Physics-Dude/Phys-Index-EyetrackVR-HW/Gum Stick Remix for 3x ESPs plus USB Hub/Adafruit USB Hub (Latest Version)/Prototypes (Work In Progress)/GSR-Adafruit_Lid-Cover-USB (M3x20mm).3mf

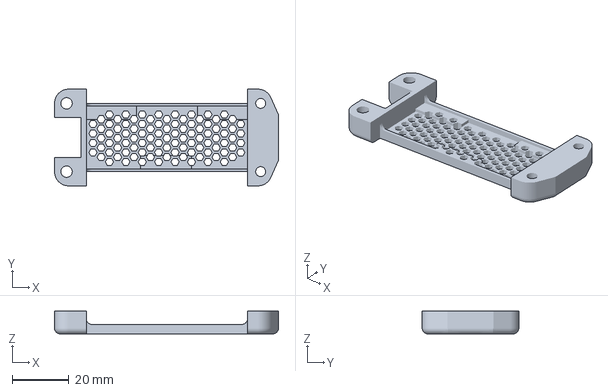
[picture p15: CAD file, 2025-03-30]
Gum Stick Remix for 3x ESPs plus USB Hub/Adafruit USB Hub (Latest Version)/Prototypes (Work In Progress)/GSR-Adafruit_Lid-Cover-USB (M3x20mm).3mf
78.8 x 34.0 x 8.00 mm
