Physics-Dude/Phys-Index-EyetrackVR-HW/Gum Stick Remix for 3x ESPs plus USB Hub/Frunk Holder (Use M3x14mm Lid)/GSR-Frunk_Brace_NoCam.3mf

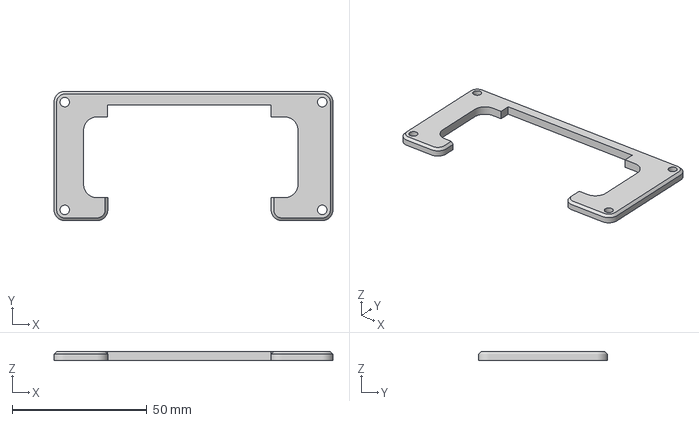
[picture p16: CAD file, 2025-03-11]
Gum Stick Remix for 3x ESPs plus USB Hub/Frunk Holder (Use M3x14mm Lid)/GSR-Frunk_Brace_NoCam.3mf
103.6 x 48.0 x 3.32 mm
