Physics-Dude/Phys-Index-EyetrackVR-HW/Gum Stick Remix for 3x ESPs plus USB Hub/Origional GSR Design (Cheap USB Hub)/GSR-Origional_Hub-Frame.3mf

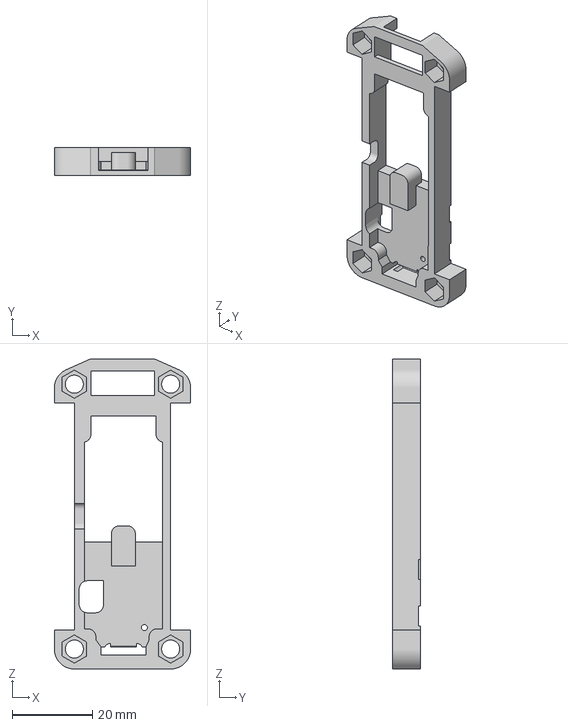
[picture p17: CAD file, 2025-03-11]
Gum Stick Remix for 3x ESPs plus USB Hub/Origional GSR Design (Cheap USB Hub)/GSR-Origional_Hub-Frame.3mf
34.0 x 7.00 x 77.3 mm
