Physics-Dude/Phys-Index-EyetrackVR-HW/Babble Face Tracker Cam-LED Mount/EXTENDED Face Mount arm v4 PRINT ME.stl

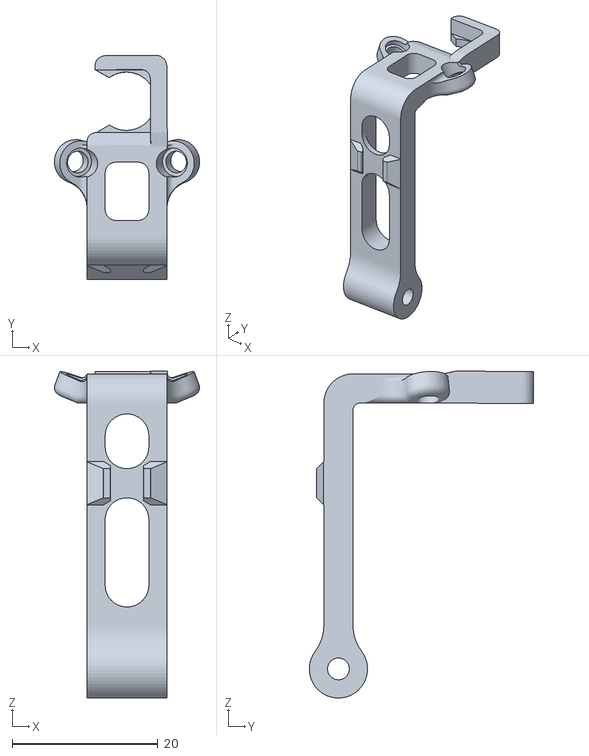
[picture p18: CAD file, 2023-12-08]
Babble Face Tracker Cam-LED Mount/EXTENDED Face Mount arm v4 PRINT ME.stl
19.9 x 30.8 x 44.9
