Physics-Dude/Phys-Index-EyetrackVR-HW/ETVR ValveIndex Cam-LED Mount Rings/Index-EyetrackVRv4 v18.step

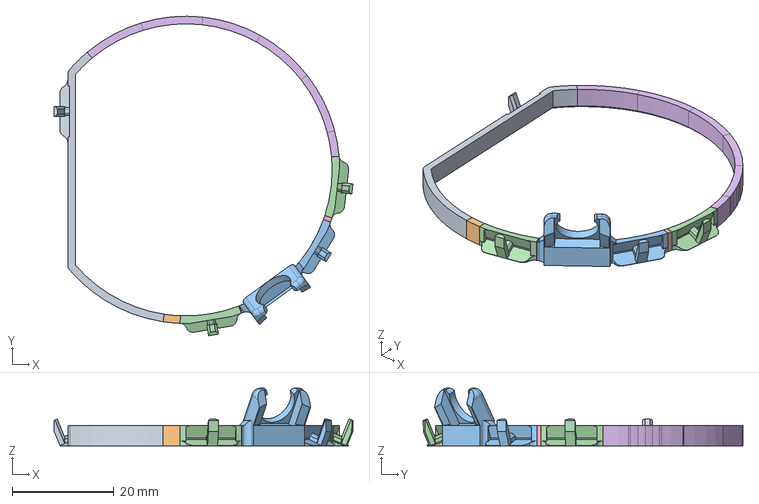
[picture p20: CAD file, 2023-10-20]
ETVR ValveIndex Cam-LED Mount Rings/Index-EyetrackVRv4 v18.step
58.9 x 62.9 x 11.4 mm
