Physics-Dude/Phys-Index-EyetrackVR-HW/Gum Stick Dongle Custom USB Hub Case/XIAO-ESP32S3 ETVR v4 gum stick index mount v22.step

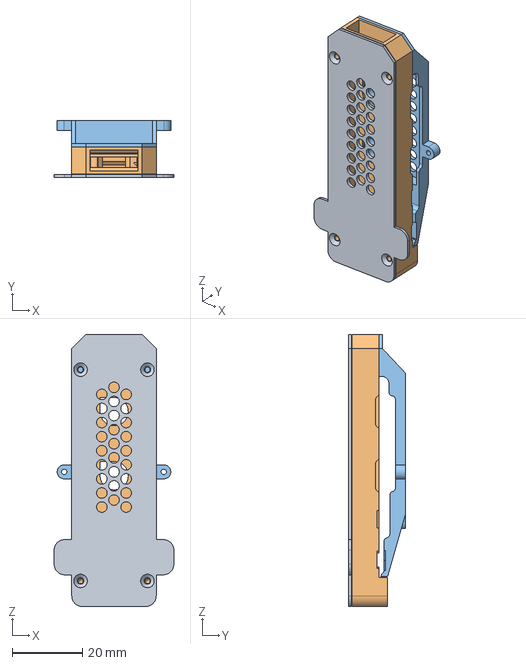
[picture p21: CAD file, 2023-10-27]
Gum Stick Dongle Custom USB Hub Case/XIAO-ESP32S3 ETVR v4 gum stick index mount v22.step
34.0 x 16.1 x 77.2 mm
