Physics-Dude/Phys-Index-EyetrackVR-HW/Gum Stick Remix for 3x ESPs plus USB Hub/Adafruit USB Hub (Latest Version)/GSR-Adafruit_Lid-Cover-Fill (M3x14mm).3mf

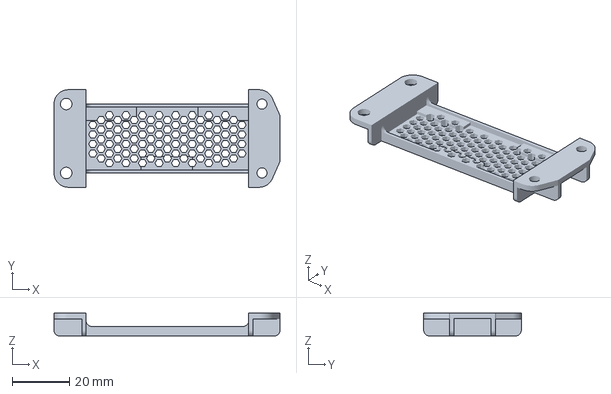
[picture p22: CAD file, 2025-03-30]
Gum Stick Remix for 3x ESPs plus USB Hub/Adafruit USB Hub (Latest Version)/GSR-Adafruit_Lid-Cover-Fill (M3x14mm).3mf
78.8 x 34.0 x 8.00 mm
