Physics-Dude/Phys-Index-EyetrackVR-HW/Gum Stick Remix for 3x ESPs plus USB Hub/Adafruit USB Hub (Latest Version)/Prototypes (Work In Progress)/GSR-Adafruit_Lid-USB-C (M3x14mm).3mf

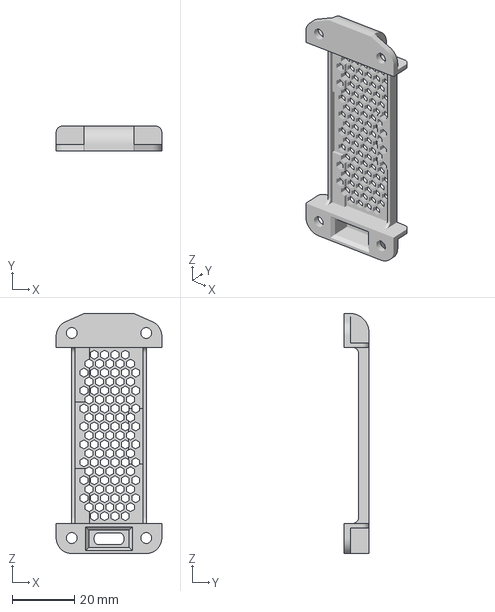
[picture p23: CAD file, 2025-03-11]
Gum Stick Remix for 3x ESPs plus USB Hub/Adafruit USB Hub (Latest Version)/Prototypes (Work In Progress)/GSR-Adafruit_Lid-USB-C (M3x14mm).3mf
34.0 x 8.00 x 77.3 mm
