Physics-Dude/Phys-Index-EyetrackVR-HW/Gum Stick Remix for 3x ESPs plus USB Hub/Frunk Holder (Use M3x14mm Lid)/GSR-Frunk_Brace_WithCam.3mf

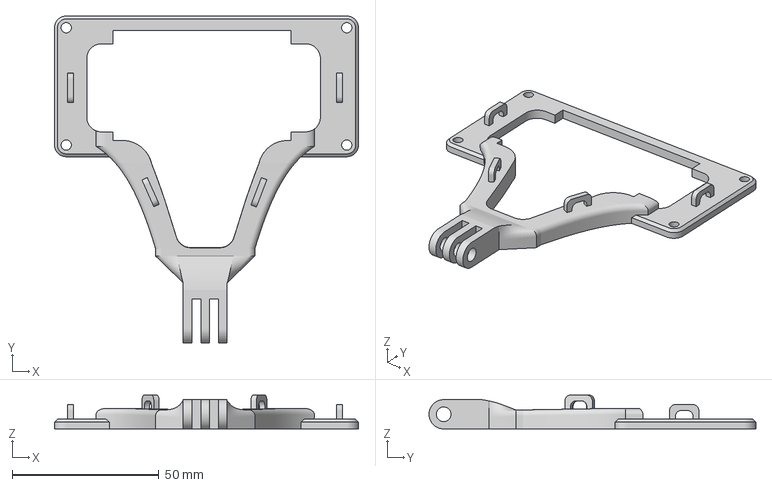
[picture p24: CAD file, 2025-03-11]
Gum Stick Remix for 3x ESPs plus USB Hub/Frunk Holder (Use M3x14mm Lid)/GSR-Frunk_Brace_WithCam.3mf
103.6 x 111.5 x 11.6 mm
