Physics-Dude/Phys-Index-EyetrackVR-HW/Babble Face Tracker Cam-LED Mount/FACE MOUNT v4 - PRINT ME with support.stl

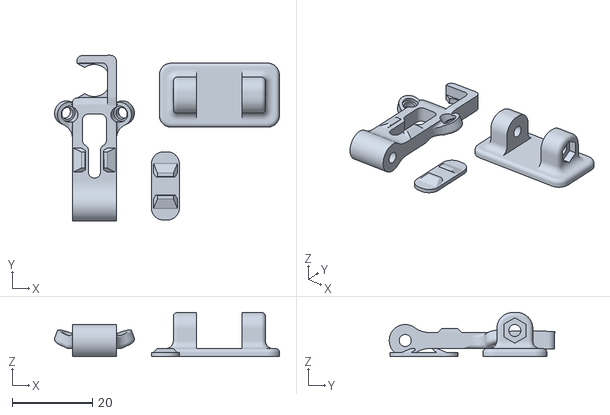
[picture p26: CAD file, 2023-12-06]
Babble Face Tracker Cam-LED Mount/FACE MOUNT v4 - PRINT ME with support.stl
56.1 x 41.3 x 11.0
