Physics-Dude/Phys-Index-EyetrackVR-HW/Babble Face Tracker Cam-LED Mount/Gumstick Remix Mount (Alternative)/GSR_Babble_FaceCam_Right.3mf

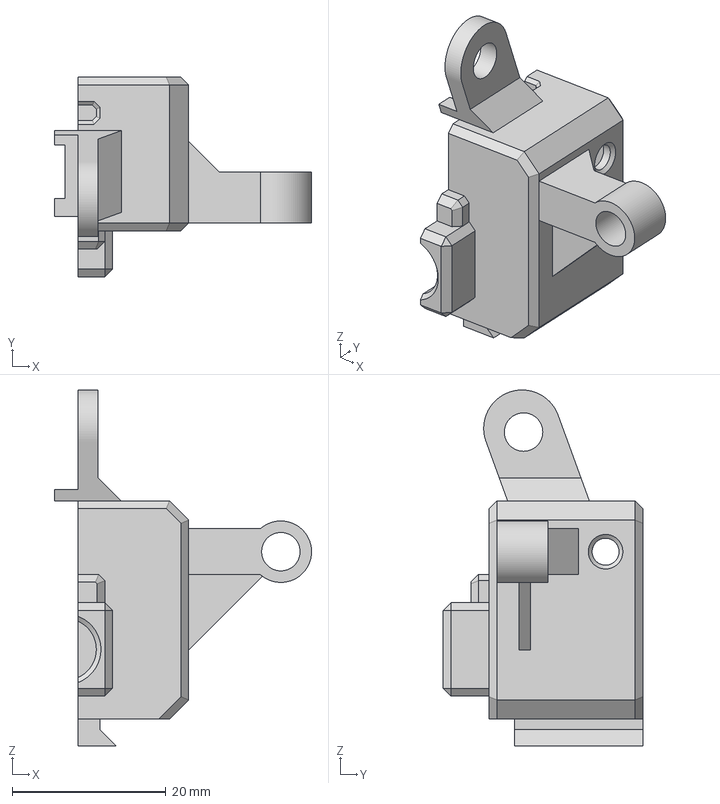
[picture p27: CAD file, 2025-03-11]
Babble Face Tracker Cam-LED Mount/Gumstick Remix Mount (Alternative)/GSR_Babble_FaceCam_Right.3mf
33.5 x 26.0 x 46.3 mm
