Physics-Dude/Phys-Index-EyetrackVR-HW/ETVR ValveIndex Cam-LED Mount Rings/Index-EyetrackVRv4 v18 Print Me.stl

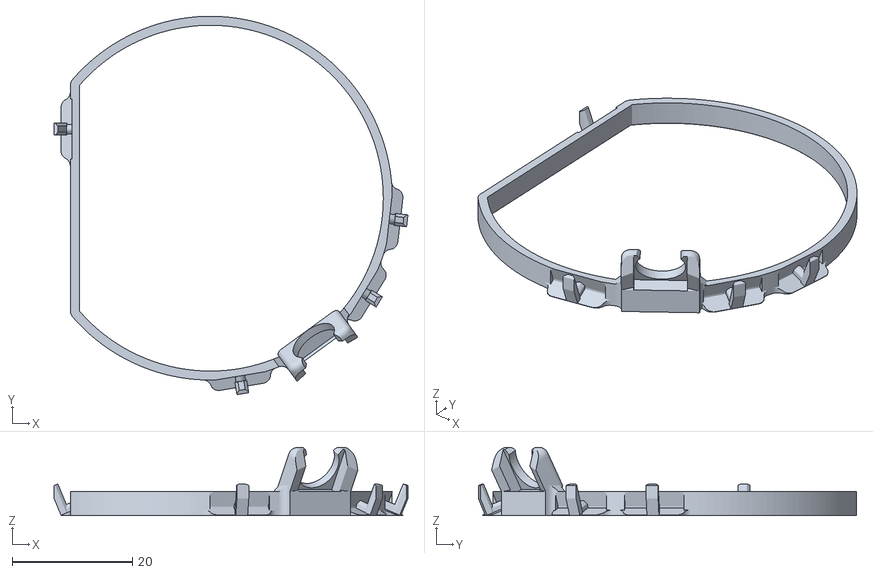
[picture p28: CAD file, 2023-10-20]
ETVR ValveIndex Cam-LED Mount Rings/Index-EyetrackVRv4 v18 Print Me.stl
58.9 x 62.9 x 11.3
