Physics-Dude/Phys-Index-EyetrackVR-HW/Gum Stick Remix for 3x ESPs plus USB Hub/Adafruit USB Hub (Latest Version)/GSR-Adafruit_ESP-Frame-Strong.3mf

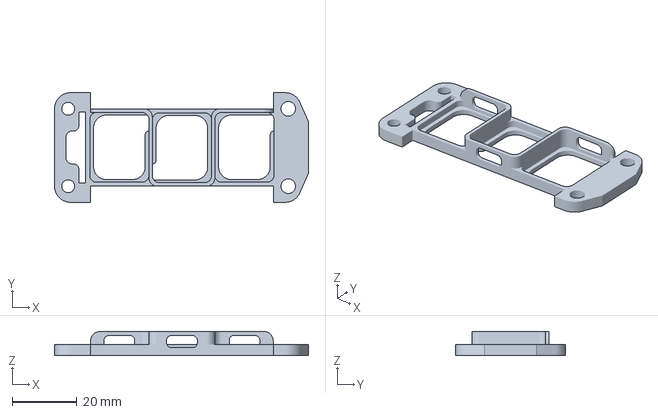
[picture p29: CAD file, 2025-03-30]
Gum Stick Remix for 3x ESPs plus USB Hub/Adafruit USB Hub (Latest Version)/GSR-Adafruit_ESP-Frame-Strong.3mf
78.8 x 34.0 x 7.50 mm
