Physics-Dude/Phys-Index-EyetrackVR-HW/Gum Stick Remix for 3x ESPs plus USB Hub/Adafruit USB Hub (Latest Version)/GSR-Adafruit_Spacer-Frame.3mf

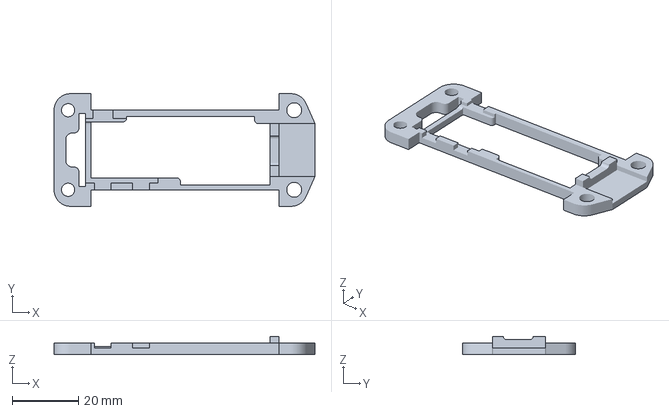
[picture p30: CAD file, 2025-03-30]
Gum Stick Remix for 3x ESPs plus USB Hub/Adafruit USB Hub (Latest Version)/GSR-Adafruit_Spacer-Frame.3mf
78.8 x 34.0 x 5.50 mm
