Physics-Dude/Phys-Index-EyetrackVR-HW/Gum Stick Remix for 3x ESPs plus USB Hub/Adafruit USB Hub (Latest Version)/GSR-Adafruit_INS-Hub-Frame.3mf

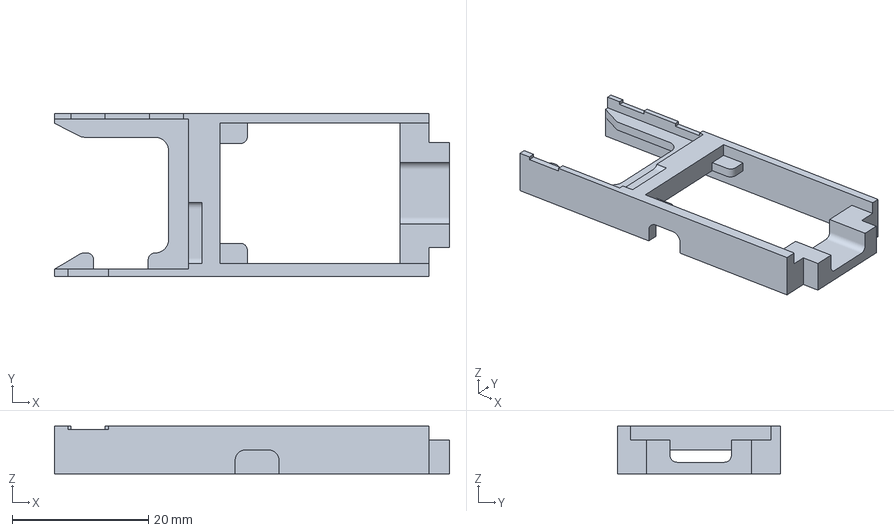
[picture p32: CAD file, 2025-03-30]
Gum Stick Remix for 3x ESPs plus USB Hub/Adafruit USB Hub (Latest Version)/GSR-Adafruit_INS-Hub-Frame.3mf
58.0 x 24.0 x 7.00 mm
